ElectronicsTinkerer/Power-Control-Panel/3D-cad/Front-Panel-Rear-Plate-Unfold.dxf

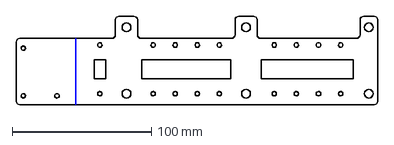
[picture p19: CAD file, 2026-03-07]
3D-cad/Front-Panel-Rear-Plate-Unfold.dxf
259.4 x 63.5 mm
