ElectronicsTinkerer/Power-Control-Panel/3D-cad/Front-Panel-Unfold.dxf

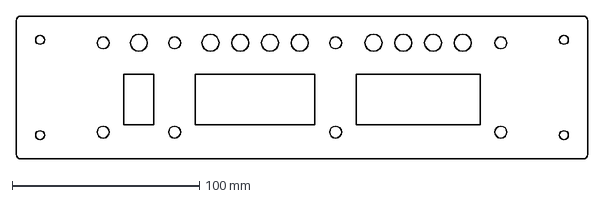
[picture p20: CAD file, 2026-03-07]
3D-cad/Front-Panel-Unfold.dxf
304.8 x 76.2 mm
