ElectronicsTinkerer/Power-Control-Panel/3D-cad/Paddle-Switch-Bracket-Cut.step

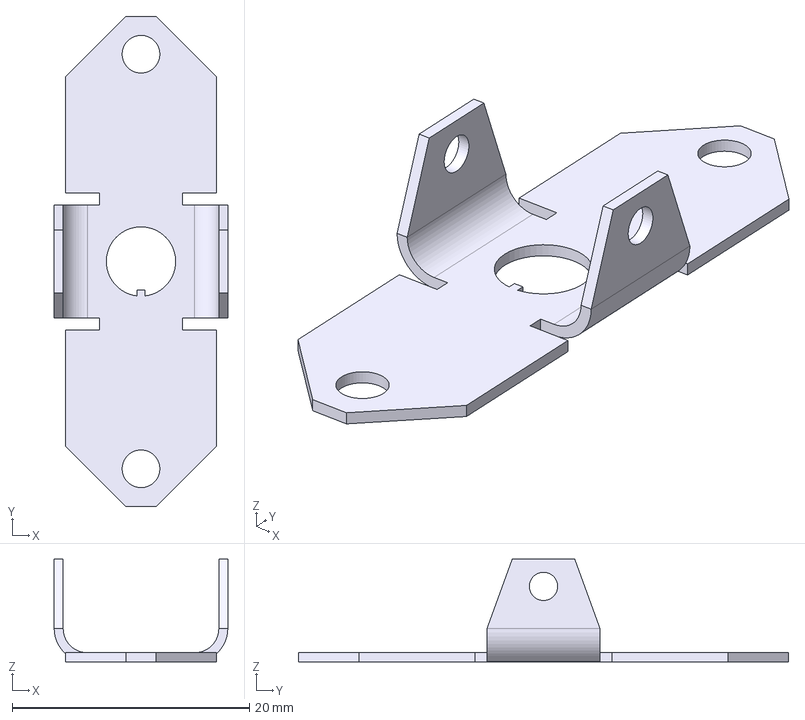
[picture p21: CAD file, 2026-02-28]
3D-cad/Paddle-Switch-Bracket-Cut.step
14.6 x 41.3 x 8.64 mm
