ElectronicsTinkerer/Power-Control-Panel/3D-cad/Paddle-Switch-Cut.step

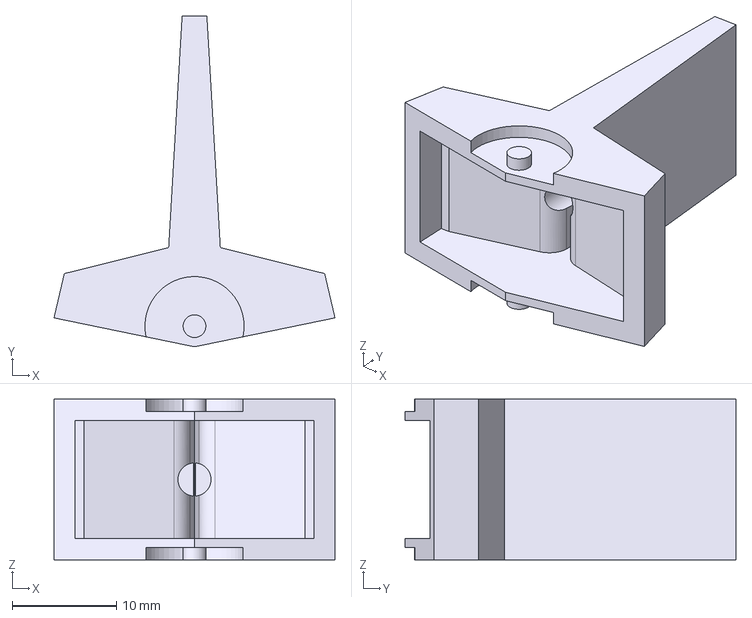
[picture p22: CAD file, 2026-02-28]
3D-cad/Paddle-Switch-Cut.step
27.0 x 31.8 x 15.4 mm
